MrTG1B/Handy/Design/STL_Files/Whippletree.stl

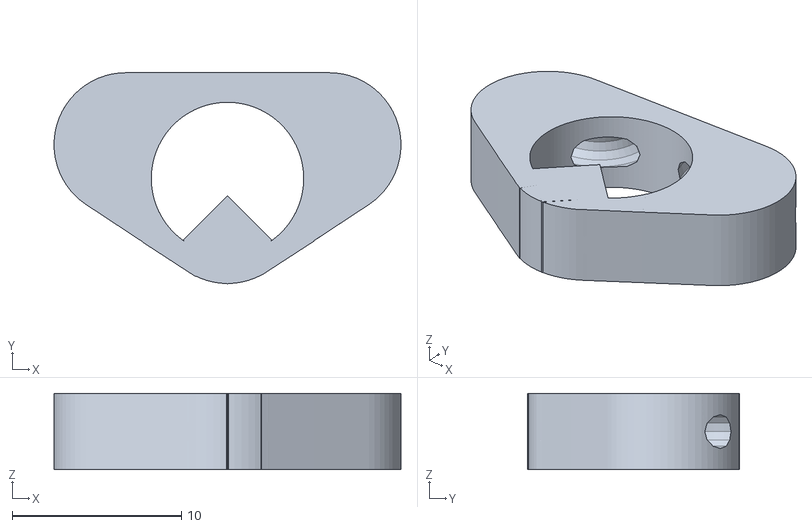
[picture p16: CAD file, 2025-05-12]
Design/STL_Files/Whippletree.stl
20.5 x 12.5 x 4.51
