MrTG1B/Handy/Design/STL_Files/Swivel pin right.stl

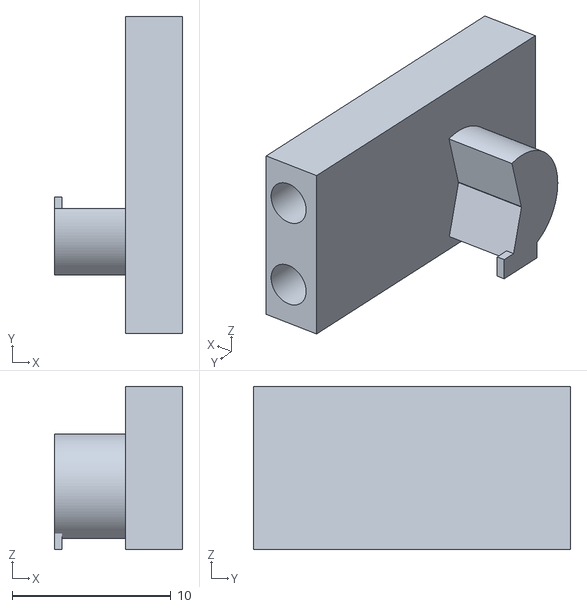
[picture p17: CAD file, 2025-05-12]
Design/STL_Files/Swivel pin right.stl
8.10 x 20.0 x 10.3
