MrTG1B/Handy/Design/STL_Files/Palm mesh right thick.stl

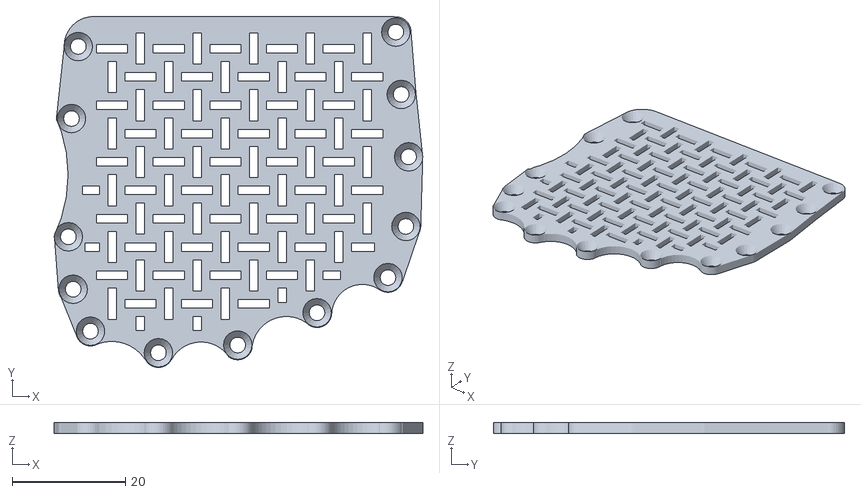
[picture p18: CAD file, 2025-05-12]
Design/STL_Files/Palm mesh right thick.stl
65.0 x 61.9 x 2.00
