MrTG1B/Handy/Design/STL_Files/Thumbtip.stl

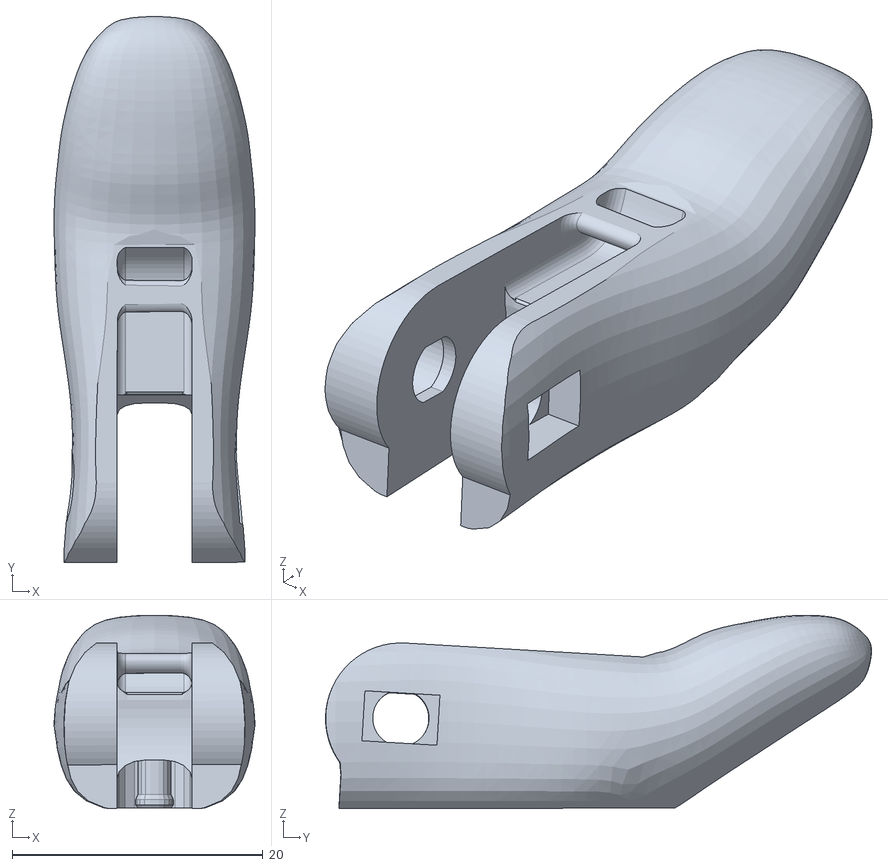
[picture p19: CAD file, 2025-05-12]
Design/STL_Files/Thumbtip.stl
16.0 x 43.6 x 15.4
