MrTG1B/Handy/Design/STL_Files/Thermo gauntlet two strap one_row.stl

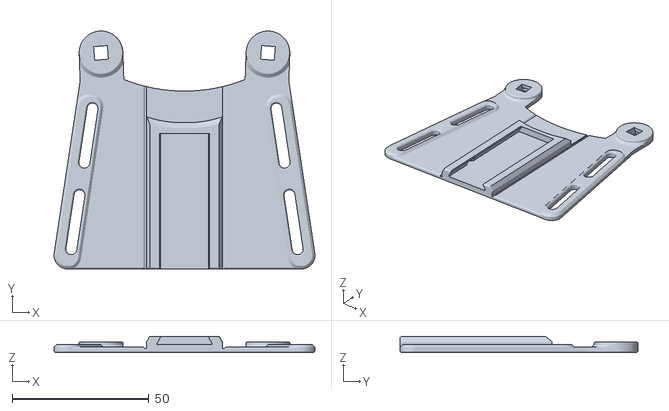
[picture p20: CAD file, 2025-05-12]
Design/STL_Files/Thermo gauntlet two strap one_row.stl
95.4 x 87.0 x 6.00
