MrTG1B/Handy/Design/STL_Files/Fingertip long.stl

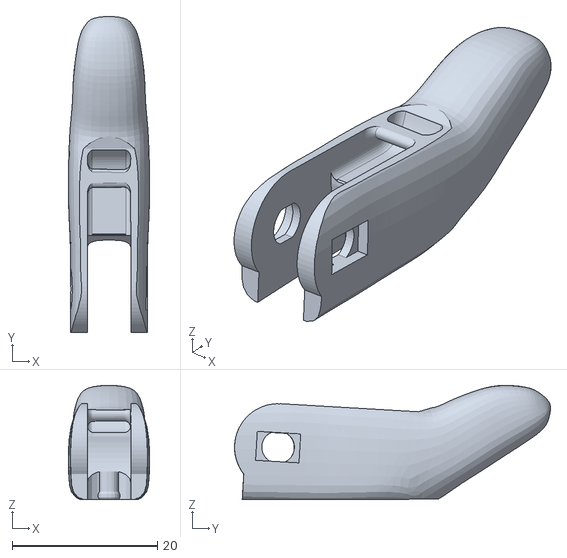
[picture p21: CAD file, 2025-05-12]
Design/STL_Files/Fingertip long.stl
11.2 x 43.6 x 15.8
