MrTG1B/Handy/Design/STL_Files/Thumb tensioner pin.stl

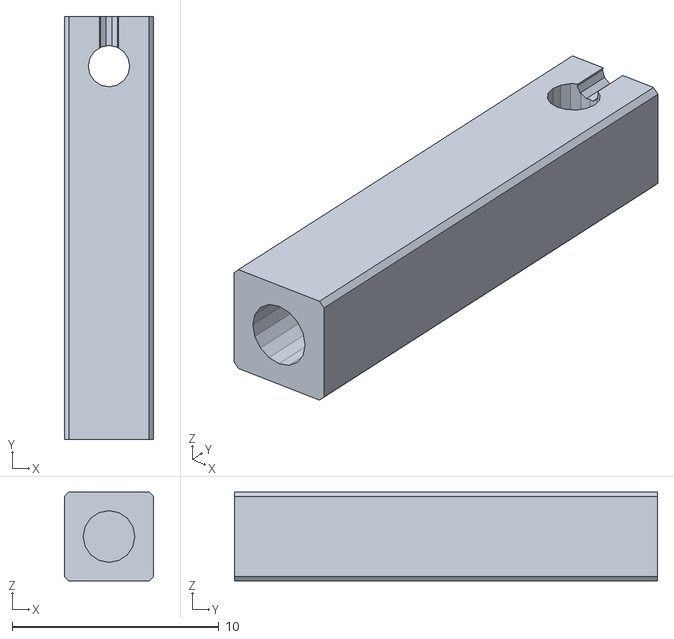
[picture p22: CAD file, 2025-05-12]
Design/STL_Files/Thumb tensioner pin.stl
4.30 x 20.4 x 4.30
